LarsEsDoch/kyndora/firmware/include/FreeSansBold36pt7b.h

#pragma once
#include <Arduino.h>
#include <gfxfont.h>

const uint8_t DejaVuSans_Bold36pt7bBitmaps[] PROGMEM = {
  0x00, 0xFF, 0xFF, 0xFF, 0xFF, 0xFF, 0xFF, 0xFF, 0xFF, 0xFF, 0xFF, 0xFF,
  0xFF, 0xFF, 0xFF, 0xFF, 0xFF, 0xFF, 0xFF, 0xFF, 0xFF, 0xFF, 0xFF, 0xFF,
  0xFF, 0xFF, 0xFF, 0xFF, 0xFF, 0xFF, 0xFF, 0xFF, 0xFF, 0xFF, 0xFF, 0xFF,
  0xFF, 0xFF, 0xF7, 0xFE, 0x7F, 0xE7, 0xFE, 0x7F, 0xE7, 0xFE, 0x7F, 0xE7,
  0xFE, 0x7F, 0xE3, 0xFC, 0x3F, 0xC0, 0x00, 0x00, 0x00, 0x00, 0x00, 0x00,
  0x00, 0xFF, 0xFF, 0xFF, 0xFF, 0xFF, 0xFF, 0xFF, 0xFF, 0xFF, 0xFF, 0xFF,
  0xFF, 0xFF, 0xFF, 0xFF, 0xFF, 0xFF, 0xFF, 0xFF, 0x01, 0xFF, 0xFE, 0x03,
  0xFF, 0xFC, 0x07, 0xFF, 0xF8, 0x0F, 0xFF, 0xF0, 0x1F, 0xFF, 0xE0, 0x3F,
  0xFF, 0xC0, 0x7F, 0xFF, 0x80, 0xFF, 0xFF, 0x01, 0xFF, 0xFE, 0x03, 0xFF,
  0xFC, 0x07, 0xFF, 0xF8, 0x0F, 0xFF, 0xF0, 0x1F, 0xFF, 0xE0, 0x3F, 0xFF,
  0xC0, 0x7F, 0xFF, 0x80, 0xFF, 0xFF, 0x01, 0xFF, 0xFE, 0x03, 0xFF, 0xFC,
  0x07, 0xF8, 0x00, 0x00, 0x1F, 0xE0, 0x0F, 0xF0, 0x00, 0x00, 0x07, 0xF0,
  0x03, 0xF8, 0x00, 0x00, 0x03, 0xFC, 0x01, 0xFE, 0x00, 0x00, 0x00, 0xFF,
  0x00, 0x7F, 0x80, 0x00, 0x00, 0x3F, 0xC0, 0x1F, 0xE0, 0x00, 0x00, 0x0F,
  0xE0, 0x07, 0xF0, 0x00, 0x00, 0x07, 0xF8, 0x03, 0xFC, 0x00, 0x00, 0x01,
  0xFE, 0x00, 0xFF, 0x00, 0x00, 0x00, 0x7F, 0x80, 0x3F, 0xC0, 0x00, 0x00,
  0x1F, 0xC0, 0x0F, 0xE0, 0x00, 0x00, 0x0F, 0xF0, 0x07, 0xF8, 0x00, 0x00,
  0x03, 0xFC, 0x01, 0xFE, 0x00, 0x00, 0x00, 0xFF, 0x00, 0x7F, 0x80, 0x03,
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
  {  8165,  36,  52,  49,    7,  -51 },   // 0x46 'F'
  {  8399,  50,  54,  58,    4,  -52 },   // 0x47 'G'
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

const GFXfont DejaVuSans_Bold36pt7b PROGMEM = {
  (uint8_t  *)DejaVuSans_Bold36pt7bBitmaps,
  (GFXglyph *)DejaVuSans_Bold36pt7bGlyphs,
  0x20, 0x7E, 82 };
