LarsEsDoch/kyndora/firmware/include/icons.h

#pragma once
#include <Arduino.h>

#define WEATHER_ICON_SIZE 24

const uint8_t ICON_AIR[] PROGMEM = {
    0x00, 0x00, 0x00,
    0x00, 0x00, 0x00,
    0x00, 0x00, 0x00,
    0x00, 0x03, 0x80,
    0x00, 0x07, 0xC0,
    0x00, 0x0C, 0x60,
    0x00, 0x00, 0x60,
    0x00, 0x00, 0x60,
    0x3F, 0xFF, 0xC0,
    0x3F, 0xFF, 0x80,
    0x00, 0x00, 0x00,
    0x3F, 0xFF, 0xF0,
    0x3F, 0xFF, 0xF8,
    0x00, 0x00, 0x0C,
    0x3F, 0xF8, 0x0C,
    0x3F, 0xFC, 0x0C,
    0x00, 0x0C, 0x18,
    0x00, 0x6C, 0x10,
    0x00, 0x7C, 0x00,
    0x00, 0x38, 0x00,
    0x00, 0x00, 0x00,
    0x00, 0x00, 0x00,
    0x00, 0x00, 0x00,
    0x00, 0x00, 0x00,
};

const uint8_t ICON_CLEAR_DAY[] PROGMEM = {
    0x00, 0x00, 0x00,
    0x00, 0x18, 0x00,
    0x00, 0x18, 0x00,
    0x00, 0x18, 0x00,
    0x0C, 0x18, 0x30,
    0x0E, 0x00, 0x70,
    0x07, 0x3C, 0xE0,
    0x02, 0xFF, 0x40,
    0x01, 0xC3, 0x80,
    0x01, 0x81, 0x80,
    0x03, 0x00, 0xC0,
    0x7B, 0x00, 0xDE,
    0x7B, 0x00, 0xDE,
    0x03, 0x00, 0xC0,
    0x01, 0x81, 0x80,
    0x01, 0xC3, 0x80,
    0x02, 0xFF, 0x40,
    0x07, 0x3C, 0xE0,
    0x0E, 0x00, 0x70,
    0x0C, 0x18, 0x30,
    0x00, 0x18, 0x00,
    0x00, 0x18, 0x00,
    0x00, 0x18, 0x00,
    0x00, 0x00, 0x00,
};

const uint8_t ICON_CLOUD[] PROGMEM = {
    0x00, 0x00, 0x00,
    0x00, 0x00, 0x00,
    0x00, 0x00, 0x00,
    0x00, 0x00, 0x00,
    0x00, 0x7E, 0x00,
    0x00, 0xFF, 0x00,
    0x01, 0xC3, 0x80,
    0x03, 0x00, 0xC0,
    0x07, 0x00, 0xE0,
    0x0E, 0x00, 0x60,
    0x1E, 0x00, 0x60,
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
    0x07, 0x00, 0xE0,
    0x03, 0x00, 0xC0,
    0x03, 0x00, 0xC0,
    0x01, 0x81, 0x80,
    0x01, 0xC3, 0x80,
    0x00, 0xC3, 0x00,
    0x00, 0x66, 0x00,
    0x00, 0x7E, 0x00,
    0x00, 0x3C, 0x00,
    0x00, 0x18, 0x00,
    0x00, 0x18, 0x00,
    0x00, 0x00, 0x00,
    0x00, 0x00, 0x00,
};
