LarsEsDoch/kyndora/backend/models.py

import secrets
from datetime import UTC, datetime, timedelta
from uuid import UUID, uuid4

from sqlalchemy import JSON
from sqlmodel import Column, Field, SQLModel


class User(SQLModel, table=True):
    __tablename__ = "users"
    id: UUID = Field(default_factory=uuid4, primary_key=True)
    username: str = Field(index=True, unique=True)
    password_hash: str
    partner_id: UUID | None = Field(default=None, foreign_key="users.id")

    latitude: float | None = Field(default=None)
    longitude: float | None = Field(default=None)
    location_updated_at: datetime | None = Field(default=None)

    timezone_auto_detect: bool = Field(default=True)
    iana_timezone: str | None = Field(default=None)

    mood: str | None = Field(default=None)
    is_sleeping: bool = Field(default=False)
    status_updated_at: datetime | None = Field(default=None)

    return_time: datetime | None = Field(default=None)

    last_seen_at: datetime | None = Field(default=None)


class Device(SQLModel, table=True):
    __tablename__ = "devices"
    mac_address: str = Field(primary_key=True)
    name: str = Field(default="Kyndora")
    user_id: UUID = Field(foreign_key="users.id")
    uptime_s: int | None = None
    firmware_version: str | None = None
    status: str = Field(default="offline")
    battery_level: int | None = None
    last_seen_at: datetime | None = None
    timezone: str | None = Field(default="CET-1CEST,M3.5.0,M10.5.0/3")


class DeviceSettings(SQLModel, table=True):
    __tablename__ = "device_settings"
    mac_address: str = Field(foreign_key="devices.mac_address", primary_key=True)

    show_date_if_not_today: bool = Field(default=True)
    show_wifi: bool = Field(default=True)
    show_time: bool = Field(default=True)
    show_weather: bool = Field(default=True)
    show_sunrise_sunset: bool = Field(default=True)
    show_daily_message: bool = Field(default=True)
    show_tamagotchi: bool = Field(default=True)
    show_doodle: bool = Field(default=True)
    show_countdown: bool = Field(default=True)
    show_live_location: bool = Field(default=True)

    led_enabled: bool = Field(default=True)
    led_brightness: int = Field(default=80)
    adaptive_brightness: bool = Field(default=True)
    night_mode: bool = Field(default=False)
    night_brightness: int = Field(default=10)

    auto_update: bool = Field(default=True)
    update_hour: int = Field(default=3)
    update_minute: int = Field(default=0)

    updated_at: datetime = Field(default_factory=lambda: datetime.now(UTC))


class MorningQuoteSettings(SQLModel, table=True):
    __tablename__ = "morning_quote_settings"
    user_id: UUID = Field(foreign_key="users.id", primary_key=True)
    wake_hour: int = Field(default=7)
    wake_minute: int = Field(default=0)
    quotes: list[str] = Field(default_factory=list, sa_column=Column(JSON))
    updated_at: datetime = Field(default_factory=lambda: datetime.now(UTC))


class ProvisioningTicket(SQLModel, table=True):
    __tablename__ = "provisioning_tickets"
    ticket_token: str = Field(
        default_factory=lambda: secrets.token_hex(16), primary_key=True
    )
    user_id: UUID = Field(foreign_key="users.id")
    expires_at: datetime = Field(
        default_factory=lambda: datetime.now(UTC) + timedelta(minutes=15)
    )


class PartnerRequest(SQLModel, table=True):
    __tablename__ = "partner_requests"
    id: int | None = Field(default=None, primary_key=True)
    sender_id: UUID = Field(foreign_key="users.id")
    receiver_id: UUID = Field(foreign_key="users.id")
    status: str = Field(default="pending")
    created_at: datetime = Field(default_factory=lambda: datetime.now(UTC))


class ContentFeed(SQLModel, table=True):
    __tablename__ = "content_feed"
    id: int | None = Field(default=None, primary_key=True)
    sender_id: UUID = Field(foreign_key="users.id")
    receiver_id: UUID = Field(foreign_key="users.id")
    content_type: str
    payload: str
    is_displayed: bool = Field(default=False)
    created_at: datetime = Field(default_factory=lambda: datetime.now(UTC))


class Telemetry(SQLModel, table=True):
    __tablename__ = "telemetry"
    id: int | None = Field(default=None, primary_key=True)
    device_mac: str = Field(foreign_key="devices.mac_address", index=True)
    rssi: int | None = None
    ssid: str | None = None
    free_heap: int | None = None
    core_temp: float | None = None
    battery_v: float | None = None
    battery_percent: int | None = None
    created_at: datetime = Field(default_factory=lambda: datetime.now(UTC), index=True)


class PushToken(SQLModel, table=True):
    __tablename__ = "push_tokens"
    id: int | None = Field(default=None, primary_key=True)
    user_id: UUID = Field(foreign_key="users.id", index=True)
    platform: str
    token: str
    created_at: datetime = Field(default_factory=lambda: datetime.now(UTC))
