LarsEsDoch/kyndora/firmware/src/provisioning.hpp

#pragma once
#include <Arduino.h>
#include <Preferences.h>
#include <WiFi.h>

class MyCallbacks;
class ProvisioningManager {

    friend class MyCallbacks;
public:
    static void begin();

    static void handle();

    static bool isProvisioned();

    static void reset();

    static bool isWiFiConnected() { return wifiConnected; }

    static String getSavedSSID();
    static String getSavedPassword();
    static String getSavedJWT();

    static void setReceivedData(String ssid, String pass, String token);

private:
    static void startBLEServer();
    static void stopBLEServer();
    static void connectToWiFi();
    static void exchangeTicketForCredentials();
    static void onWiFiEvent(WiFiEvent_t event);

    static Preferences preferences;

    static String tempSSID;
    static String tempPassword;
    static String tempToken;
    static bool dataReceivedReady;

    static bool provisionedState;
    static bool stateChecked;

    static volatile bool wifiConnected;
    static bool awaitingWifiForRegistration;
    static uint32_t wifiConnectAttemptStart;
    static constexpr uint32_t WIFI_CONNECT_TIMEOUT_MS = 20000;
};
