LarsEsDoch/kyndora/firmware/src/update.hpp

#pragma once
#include <Preferences.h>
#include "display_manager.h"

class UpdateManager {
public:
    explicit UpdateManager(const String& buildVersion, const String& channel, const int& checkUpdateHour, DisplayManager& display);

    void begin();
    void automaticCheckForUpdates();
    void checkForUpdates();
    void executeOTA(const String& newVersion);

    bool hasUpdateError() const { return updateError; }

private:
    DisplayManager& _displayManager;
    int updateHour;
    int lastCheckDay = -1;

    String channel;
    String appliedVersion;
    String initialBuildVersion;
    String downloadUrl;

    bool updateError = false;

    Preferences preferences;

    String buildApiUrl() const;
    String loadAppliedVersion(const String& buildVersion);
    void saveAppliedVersion(const String& version);

    static bool isWiFiConnected();
};
