LarsEsDoch/kyndora/backend/security.py

import os
from datetime import UTC, datetime, timedelta
from uuid import UUID

import jwt
from argon2 import PasswordHasher
from dotenv import load_dotenv
from fastapi import Depends, HTTPException, status
from fastapi.security import OAuth2PasswordBearer
from sqlmodel import Session

from database import get_session
from models import User

ph = PasswordHasher()


def get_password_hash(password: str) -> str:
    return ph.hash(password)


def verify_password(plain_password: str, hashed_password: str) -> bool:
    try:
        return ph.verify(hashed_password, plain_password)
    except Exception:
        return False


load_dotenv()

SECRET_KEY = os.getenv("JWT_SECRET", "te!Lm&88%Ppc4YtziIW@%o!ZYxgvzVMp")
ALGORITHM = "HS256"
ACCESS_TOKEN_EXPIRE_MINUTES = 60 * 24 * 30


def create_access_token(data: dict, expires_delta: timedelta | None = None):
    to_encode = data.copy()
    expire = datetime.now(UTC) + (
        expires_delta or timedelta(minutes=ACCESS_TOKEN_EXPIRE_MINUTES)
    )
    to_encode.update({"exp": expire})
    return jwt.encode(to_encode, SECRET_KEY, algorithm=ALGORITHM)


oauth2_scheme = OAuth2PasswordBearer(tokenUrl="auth/login")


def get_current_user_id(token: str = Depends(oauth2_scheme)) -> UUID:
    credentials_exception = HTTPException(
        status_code=status.HTTP_401_UNAUTHORIZED,
        detail="Konnte Zugangsdaten nicht validieren",
        headers={"WWW-Authenticate": "Bearer"},
    )
    try:
        payload = jwt.decode(token, SECRET_KEY, algorithms=[ALGORITHM])
        user_id_str: str = payload.get("sub")
        if user_id_str is None:
            raise credentials_exception
        return UUID(user_id_str)
    except jwt.ExpiredSignatureError:
        raise HTTPException(status_code=401, detail="Token ist abgelaufen")
    except jwt.PyJWTError:
        raise credentials_exception


def get_current_user(
    user_id: UUID = Depends(get_current_user_id),
    session: Session = Depends(get_session),
) -> User:
    user = session.get(User, user_id)
    if not user:
        raise HTTPException(
            status_code=status.HTTP_401_UNAUTHORIZED, detail="User nicht gefunden"
        )
    return user


def decode_token_to_user_id(token: str) -> UUID:
    try:
        payload = jwt.decode(token, SECRET_KEY, algorithms=[ALGORITHM])
        user_id_str: str = payload.get("sub")
        if user_id_str is None:
            raise ValueError("Token has no subject")
        return UUID(user_id_str)
    except jwt.PyJWTError:
        raise ValueError("Invalid token")
    except (ValueError, TypeError):
        raise ValueError("Invalid token")
